schlae/a1000-scsi-sidecar/SCSISidecar.kicad_sch

## KiCad design SCSISidecar.kicad_sch (2025-05-16, an earlier design)

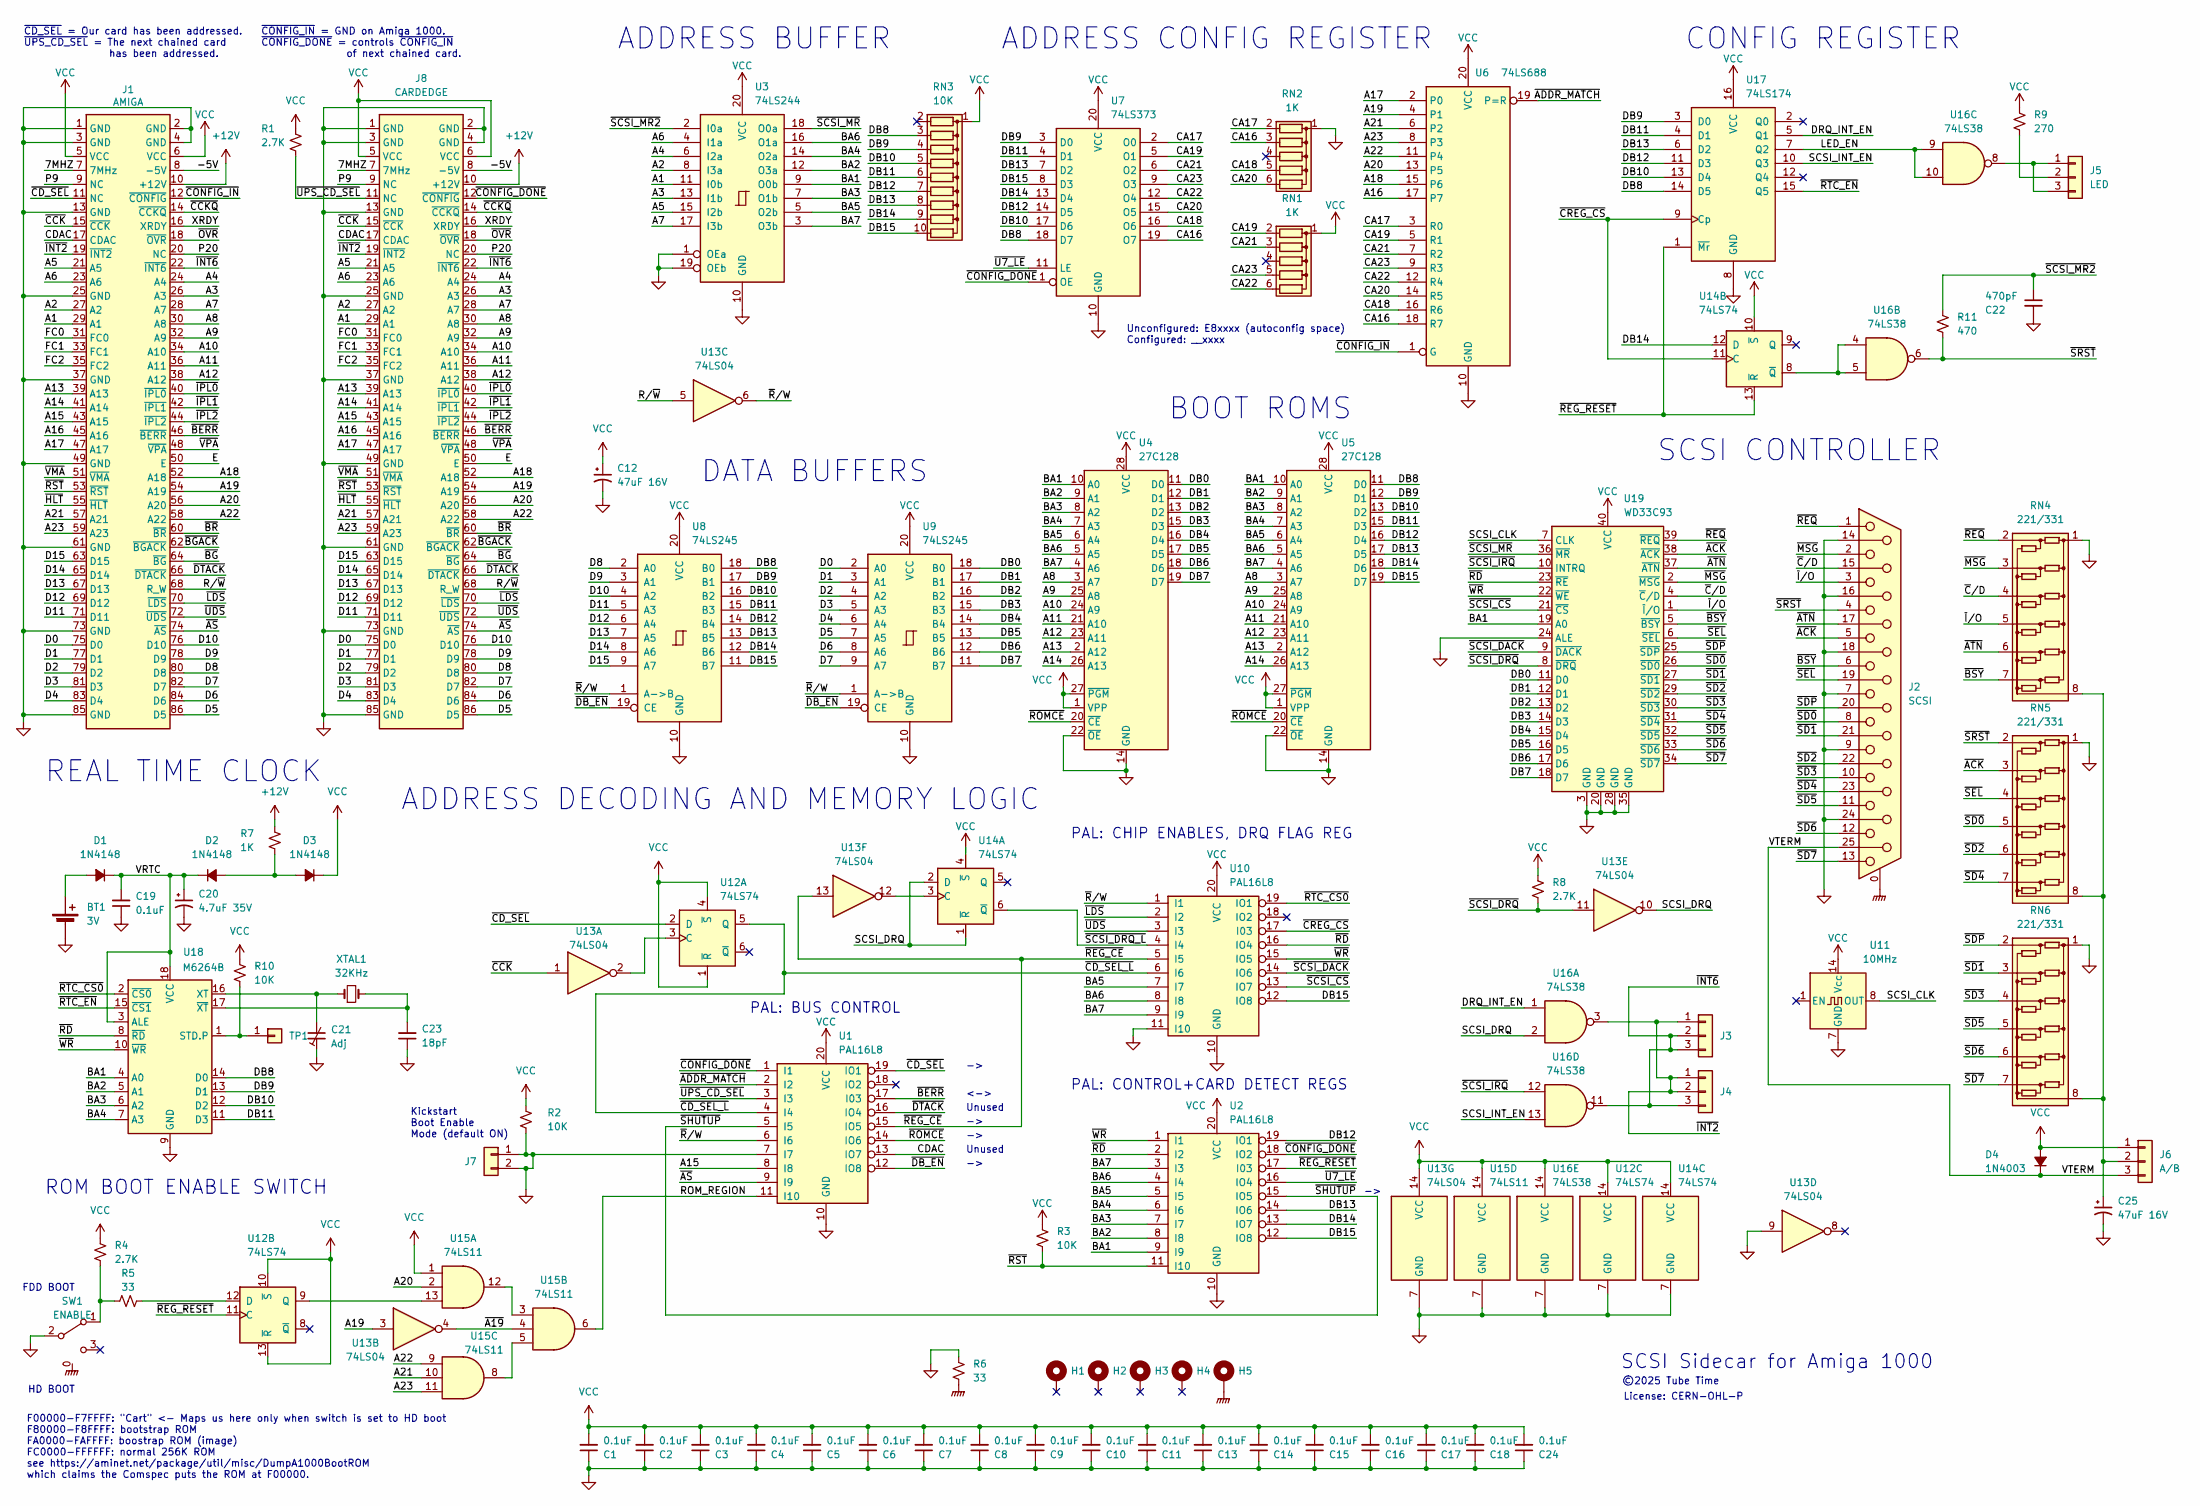
[picture p6: schematic SCSISidecar.kicad_sch]

Parts:
BT1: 3V; BatteryHolder_Keystone_104_1x23mm; MPN Keystone 104
C1, C2, C3, C4, C5, C6, C7, C8, C9, C10, C11, C13, C14, C15, C16, C17, C18, C19, C24: 0.1uF; CAPAC200
C12, C25: 47uF 16V; CAPAE200P500X1100
C20: 4.7uF 35V; CAPAE200P500X1100
C21: Adj; TRIM_CAP
C22: 470pF; CAPAC200
C23: 18pF; C_Disc_D3.0mm_W1.6mm_P2.50mm
D1, D2, D3: 1N4148; DIOA500
D4: 1N4003; DIOA500
H1, H2, H3, H4, H5: MountingHole_Pad; MountingHole_3.7mm_Pad
J1: AMIGA; TE_1-5530843-0; MPN TE 1-5530843-0 or equiv
J2: SCSI; DSUB-25_Female_Horizontal_P2.77x2.84mm_EdgePinOffset7.70mm_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
J3, J4: Conn_01x03; PinHeader_1x03_P2.54mm_Vertical
J5: LED; PinHeader_1x03_P2.54mm_Vertical
J6: A/B; PinHeader_1x03_P2.54mm_Vertical
J7: Conn_01x02; PinHeader_1x02_P2.54mm_Vertical
J8: CARDEDGE; PinHeader_2x43_P2.54mm_Vertical
R1, R4, R8: 2.7K; R_Axial_L0.26in_D0.92in_P0.5in_Horizontal
R2, R3, R10: 10K; R_Axial_L0.26in_D0.92in_P0.5in_Horizontal
R5, R6: 33; R_Axial_L0.26in_D0.92in_P0.5in_Horizontal
R7: 1K; R_Axial_L0.26in_D0.92in_P0.5in_Horizontal
R9: 270; R_Axial_L0.26in_D0.92in_P0.5in_Horizontal
R11: 470; R_Axial_L0.26in_D0.92in_P0.5in_Horizontal
RN1, RN2: 1K; R_Array_SIP6
RN3: 10K; R_Array_SIP10
RN4, RN5, RN6: 221/331; R_Array_SIP8; MPN 4608X-104-221/331L
SW1: ENABLE; SW_SPDT_RA; MPN 7101J1AV2QE2 or equiv
TP1: Conn_01x01; PinHeader_1x01_P2.54mm_Vertical
U1, U2, U10: PAL16L8; DIP254P762X635-20
U3: 74LS244; DIP254P762X635-20
U4, U5: 27C128; DIP-28_W15.24mm
U6: 74LS688; DIP254P762X635-20
U7: 74LS373; DIP254P762X635-20
U8, U9: 74LS245; DIP254P762X635-20
U11: 10MHz; Oscillator_DIP-14; MPN ECS-100AX-100 or equiv
U12, U14: 74LS74; DIP254P762X635-14
U13: 74LS04; DIP254P762X635-14
U15: 74LS11; DIP254P762X635-14
U16: 74LS38; DIP254P762X635-14
U17: 74LS174; DIP254P762X635-16
U18: M6264B; DIP254P762X635-18
U19: WD33C93; DIP254P1524X635-40
XTAL1: 32KHz; Crystal_AT310_D3.0mm_L10.0mm_Horizontal

Connections:
7MHZ: J1.7 (7MHz), J8.7 (7MHz)
+12V: J1.10 (+12V), J8.10 (+12V), R7.2
-5V: J1.8 (-5V), J8.8 (-5V)
A1: J1.29 (A1), J8.29 (A1), U3.11 (I0b)
A2: J1.27 (A2), J8.27 (A2), U3.8 (I3a)
A3: J1.26 (A3), J8.26 (A3), U3.13 (I1b)
A4: J1.24 (A4), J8.24 (A4), U3.6 (I2a)
A5: J1.21 (A5), J8.21 (A5), U3.15 (I2b)
A6: J1.23 (A6), J8.23 (A6), U3.4 (I1a)
A7: J1.28 (A7), J8.28 (A7), U3.17 (I3b)
A8: J1.30 (A8), J8.30 (A8), U4.3 (A7), U5.3 (A7)
A9: J1.32 (A9), J8.32 (A9), U4.25 (A8), U5.25 (A8)
A10: J1.34 (A10), J8.34 (A10), U4.24 (A9), U5.24 (A9)
A11: J1.36 (A11), J8.36 (A11), U4.21 (A10), U5.21 (A10)
A12: J1.38 (A12), J8.38 (A12), U4.23 (A11), U5.23 (A11)
A13: J1.39 (A13), J8.39 (A13), U4.2 (A12), U5.2 (A12)
A14: J1.41 (A14), J8.41 (A14), U4.26 (A13), U5.26 (A13)
A15: J1.43 (A15), J8.43 (A15), U1.8 (I8)
A16: J1.45 (A16), J8.45 (A16), U6.17 (P7)
A17: J1.47 (A17), J8.47 (A17), U6.2 (P0)
A18: J1.52 (A18), J8.52 (A18), U6.15 (P6)
A19: J1.54 (A19), J8.54 (A19), U6.4 (P1), U13.3
A20: J1.56 (A20), J8.56 (A20), U6.13 (P5), U15.2
A21: J1.57 (A21), J8.57 (A21), U6.6 (P2), U15.10
A22: J1.58 (A22), J8.58 (A22), U6.11 (P4), U15.9
A23: J1.59 (A23), J8.59 (A23), U6.8 (P3), U15.11
BA1: U2.9 (I9), U3.9 (O0b), U4.10 (A0), U5.10 (A0), U18.4 (A0), U19.19 (A0)
BA2: U2.8 (I8), U3.12 (O3a), U4.9 (A1), U5.9 (A1), U18.5 (A1)
BA3: U2.7 (I7), U3.7 (O1b), U4.8 (A2), U5.8 (A2), U18.6 (A2)
BA4: U2.6 (I6), U3.14 (O2a), U4.7 (A3), U5.7 (A3), U18.7 (A3)
BA5: U2.5 (I5), U3.5 (O2b), U4.6 (A4), U5.6 (A4), U10.7 (I7)
BA6: U2.4 (I4), U3.16 (O1a), U4.5 (A5), U5.5 (A5), U10.8 (I8)
BA7: U2.3 (I3), U3.3 (O3b), U4.4 (A6), U5.4 (A6), U10.9 (I9)
CA16: RN2.3 (R2), U6.18 (R7), U7.19 (O7)
CA17: RN2.2 (R1), U6.3 (R0), U7.2 (O0)
CA18: RN2.5 (R4), U6.16 (R6), U7.16 (O6)
CA19: RN1.2 (R1), U6.5 (R1), U7.5 (O1)
CA20: RN2.6 (R5), U6.14 (R5), U7.15 (O5)
CA21: RN1.3 (R2), U6.7 (R2), U7.6 (O2)
CA22: RN1.6 (R5), U6.12 (R4), U7.12 (O4)
CA23: RN1.5 (R4), U6.9 (R3), U7.9 (O3)
CDAC: J1.17 (CDAC), J8.17 (CDAC), U1.13 (IO7)
D0: J1.75 (D0), J8.75 (D0), U9.2 (A0)
D1: J1.77 (D1), J8.77 (D1), U9.3 (A1)
D2: J1.79 (D2), J8.79 (D2), U9.4 (A2)
D3: J1.81 (D3), J8.81 (D3), U9.5 (A3)
D4: J1.83 (D4), J8.83 (D4), U9.6 (A4)
D5: J1.86 (D5), J8.86 (D5), U9.7 (A5)
D6: J1.84 (D6), J8.84 (D6), U9.8 (A6)
D7: J1.82 (D7), J8.82 (D7), U9.9 (A7)
D8: J1.80 (D8), J8.80 (D8), U8.2 (A0)
D9: J1.78 (D9), J8.78 (D9), U8.3 (A1)
D10: J1.76 (D10), J8.76 (D10), U8.4 (A2)
D11: J1.71 (D11), J8.71 (D11), U8.5 (A3)
D12: J1.69 (D12), J8.69 (D12), U8.6 (A4)
D13: J1.67 (D13), J8.67 (D13), U8.7 (A5)
D14: J1.65 (D14), J8.65 (D14), U8.8 (A6)
D15: J1.63 (D15), J8.63 (D15), U8.9 (A7)
DB0: U4.11 (D0), U9.18 (B0), U19.11 (D0)
DB1: U4.12 (D1), U9.17 (B1), U19.12 (D1)
DB2: U4.13 (D2), U9.16 (B2), U19.13 (D2)
DB3: U4.15 (D3), U9.15 (B3), U19.14 (D3)
DB4: U4.16 (D4), U9.14 (B4), U19.15 (D4)
DB5: U4.17 (D5), U9.13 (B5), U19.16 (D5)
DB6: U4.18 (D6), U9.12 (B6), U19.17 (D6)
DB7: U4.19 (D7), U9.11 (B7), U19.18 (D7)
DB8: RN3.3 (R2), U5.11 (D0), U7.18 (D7), U8.18 (B0), U17.14 (D5), U18.14 (D0)
DB9: RN3.4 (R3), U5.12 (D1), U7.3 (D0), U8.17 (B1), U17.3 (D0), U18.13 (D1)
DB10: RN3.5 (R4), U5.13 (D2), U7.17 (D6), U8.16 (B2), U17.13 (D4), U18.12 (D2)
DB11: RN3.6 (R5), U5.15 (D3), U7.4 (D1), U8.15 (B3), U17.4 (D1), U18.11 (D3)
DB12: RN3.7 (R6), U2.19 (IO1), U5.16 (D4), U7.14 (D5), U8.14 (B4), U17.11 (D3)
DB13: RN3.8 (R7), U2.14 (IO6), U5.17 (D5), U7.7 (D2), U8.13 (B5), U17.6 (D2)
DB14: RN3.9 (R8), U2.13 (IO7), U5.18 (D6), U7.13 (D4), U8.12 (B6), U14.12 (D)
DB15: RN3.10 (R9), U2.12 (IO8), U5.19 (D7), U7.8 (D3), U8.11 (B7), U10.12 (IO8)
DRQ_INT_EN: U16.1, U17.5 (Q1)
E: J1.50 (E), J8.50 (E)
FC0: J1.31 (FC0), J8.31 (FC0)
FC1: J1.33 (FC1), J8.33 (FC1)
FC2: J1.35 (FC2), J8.35 (FC2)
GND: BT1.2 (-), C1.1, C2.1, C3.1, C4.1, C5.1, C6.1, C7.1, C8.1, C9.1, C10.1, C11.1, C12.2, C13.1, C14.1, C15.1, C16.1, C17.1, C18.1, C19.1, C20.2, C21.1, C22.2, C23.1, C24.1, C25.2, J1.1 (GND), J1.2 (GND), J1.3 (GND), J1.4 (GND), J1.13 (GND), J1.25 (GND), J1.37 (GND), J1.49 (GND), J1.61 (GND), J1.73 (GND), J1.85 (GND), J2.7, J2.9, J2.14, J2.16, J2.18, J2.24, J7.1, J7.2, J8.1 (GND), J8.2 (GND), J8.3 (GND), J8.4 (GND), J8.13 (GND), J8.25 (GND), J8.37 (GND), J8.49 (GND), J8.61 (GND), J8.73 (GND), J8.85 (GND), R2.1, R6.1, RN2.1 (common), RN4.1 (COM1), RN5.1 (COM1), RN6.1 (COM1), SW1.2 (B), U1.7 (I7), U1.10 (GND), U2.10 (GND), U3.1 (OEa), U3.10 (GND), U3.19 (OEb), U4.14 (GND), U4.22 (~OE), U5.14 (GND), U5.22 (~OE), U6.10 (GND), U7.10 (GND), U8.10 (GND), U9.10 (GND), U10.10 (GND), U10.11 (I10), U11.7 (GND), U12.7 (GND), U13.7 (GND), U13.9, U14.7 (GND), U15.7 (GND), U16.7 (GND), U17.8 (GND), U18.9 (GND), U19.3 (GND), U19.20 (GND), U19.24 (ALE), U19.28 (GND), U19.35 (GND)
GNDPWR: H5.1, J2.0 (PAD), R6.2, SW1.0 (SH)
LED_EN: U16.9, U16.10, U17.7 (Q2)
unnamed: BT1.1 (+), D1.2 (A)
unnamed: C21.2, U18.16 (XT), XTAL1.1
unnamed: C23.2, U18.17 (~XT), XTAL1.2
unnamed: C25.1, J6.2, RN4.8 (COM2), RN5.8 (COM2), RN6.8 (COM2)
unnamed: D2.2 (A), D3.2 (A), R7.1
unnamed: J5.1, J5.3, U16.8
unnamed: J5.2, R9.1
unnamed: R4.2, R5.2, SW1.1 (A)
unnamed: R5.1, U12.12 (D)
unnamed: R10.1, TP1.1, U18.1 (STD.P)
unnamed: U12.3 (C), U13.2
unnamed: U12.9 (Q), U15.13
unnamed: U13.12, U14.3 (C)
unnamed: U14.8 (~Q), U16.4, U16.5
unnamed: U15.5, U15.8
unnamed: U15.3, U15.12
P9: J1.9 (NC), J8.9 (NC)
P20: J1.20 (NC), J8.20 (NC)
ROM_REGION: U1.11 (I10), U15.6
R/~W: J1.68 (R_W), J8.68 (R_W), U13.5
SCSI_CLK: U11.8 (OUT), U19.7 (CLK)
SCSI_DRQ: U13.10, U14.1 (~R), U14.2 (D), U16.2
SCSI_INT_EN: U16.13, U17.10 (Q3)
VCC: C1.2, C2.2, C3.2, C4.2, C5.2, C6.2, C7.2, C8.2, C9.2, C10.2, C11.2, C12.1, C13.2, C14.2, C15.2, C16.2, C17.2, C18.2, C24.2, D3.1 (K), D4.2 (A), J1.5 (VCC), J1.6 (VCC), J6.1, J8.5 (VCC), J8.6 (VCC), R1.1, R2.2, R3.2, R4.1, R8.1, R9.2, R10.2, RN1.1 (common), RN3.1 (common), U1.20 (VCC), U2.20 (VCC), U3.20 (VCC), U4.1 (VPP), U4.27 (~PGM), U4.28 (VCC), U5.1 (VPP), U5.27 (~PGM), U5.28 (VCC), U6.20 (VCC), U7.20 (VCC), U8.20 (VCC), U9.20 (VCC), U10.20 (VCC), U11.14 (Vcc), U12.1 (~R), U12.4 (~S), U12.10 (~S), U12.13 (~R), U12.14 (VCC), U13.14 (VCC), U14.4 (~S), U14.10 (~S), U14.14 (VCC), U15.1, U15.14 (VCC), U16.14 (VCC), U17.16 (VCC), U19.40 (VCC)
VRTC: C19.2, C20.1, D1.1 (K), D2.1 (K), U18.3 (ALE), U18.18 (VCC)
VTERM: D4.1 (K), J2.25, J6.3
XRDY: J1.16 (XRDY), J8.16 (XRDY)
~A19: U13.4, U15.4
~ACK: J2.5, RN5.3 (R2), U19.38 (~ACK)
~ADDR_MATCH: U1.2 (I2), U6.19 (P=R)
~AS: J1.74 (~AS), J8.74 (~AS), U1.9 (I9)
~ATN: J2.17, RN4.6 (R5), U19.37 (~ATN)
~BERR: J1.46 (~BERR), J8.46 (~BERR), U1.17 (I03)
~BGACK: J1.62 (~BGACK), J8.62 (~BGACK)
~BG: J1.64 (~BG), J8.64 (~BG)
~BR: J1.60 (~BR), J8.60 (~BR)
~BSY: J2.6, RN4.7 (R6), U19.5 (~BSY)
~CCKQ: J1.14 (~CCKQ), J8.14 (~CCKQ)
~CCK: J1.15 (~CCK), J8.15 (~CCK), U13.1
~CD_SEL_L: U1.4 (I4), U10.6 (I6), U12.5 (Q)
~CD_SEL: J1.11 (NC), U1.19 (IO1), U12.2 (D)
~CONFIG_DONE: J8.12 (~CONFIG), U1.1 (I1), U2.18 (IO2), U7.1 (OE)
~CONFIG_IN: J1.12 (~CONFIG), U6.1 (G)
~CREG_CS: U10.17 (I03), U14.11 (C), U17.9 (Cp)
~C/D: J2.15, RN4.4 (R3), U19.4 (~C/D)
~DB_EN: U1.12 (IO8), U8.19 (CE), U9.19 (CE)
~DTACK: J1.66 (~DTACK), J8.66 (~DTACK), U1.16 (IO4)
~HLT: J1.55 (~HLT), J8.55 (~HLT)
~INT2: J1.19 (~INT2), J3.1, J4.1, J4.2, J8.19 (~INT2), U16.3
~INT6: J1.22 (~INT6), J3.2, J3.3, J4.3, J8.22 (~INT6), U16.11
~IPL0: J1.40 (~IPL0), J8.40 (~IPL0)
~IPL1: J1.42 (~IPL1), J8.42 (~IPL1)
~IPL2: J1.44 (~IPL2), J8.44 (~IPL2)
~I/O: J2.3, RN4.5 (R4), U19.1 (~I/O)
~LDS: J1.70 (~LDS), J8.70 (~LDS), U10.2 (I2)
~MSG: J2.2, RN4.3 (R2), U19.2 (~MSG)
~OVR: J1.18 (~OVR), J8.18 (~OVR)
~RD: U2.2 (I2), U10.16 (IO4), U18.8 (~RD), U19.23 (~RE)
~REG_CE: U1.15 (IO5), U10.5 (I5), U13.13
~REG_RESET: U2.17 (I03), U12.11 (C), U14.13 (~R), U17.1 (~Mr)
~REQ: J2.1, RN4.2 (R1), U19.39 (~REQ)
~ROMCE: U1.14 (IO6), U4.20 (~CE), U5.20 (~CE)
~RST: J1.53 (~RST), J8.53 (~RST), R3.1, U2.11 (I10)
~RTC_CS0: U10.19 (IO1), U18.2 (~CS0)
~RTC_EN: U17.15 (Q5), U18.15 (~CS1)
~R/W: U1.6 (I6), U8.1 (A->B), U9.1 (A->B), U10.1 (I1), U13.6
~SCSI_CS: U10.13 (IO7), U19.21 (~CS)
~SCSI_DACK: U10.14 (IO6), U19.9 (~DACK)
~SCSI_DRQ_L: U10.4 (I4), U14.6 (~Q)
~SCSI_DRQ: R8.2, U13.11, U19.8 (~DRQ)
~SCSI_IRQ: U16.12, U19.10 (INTRQ)
~SCSI_MR2: C22.1, R11.2, U3.2 (I0a)
~SCSI_MR: U3.18 (O0a), U19.36 (~MR)
~SD0: J2.8, RN5.5 (R4), U19.26 (~SD0)
~SD1: J2.21, RN6.3 (R2), U19.27 (~SD1)
~SD2: J2.22, RN5.6 (R5), U19.29 (~SD2)
~SD3: J2.10, RN6.4 (R3), U19.30 (~SD3)
~SD4: J2.23, RN5.7 (R6), U19.31 (~SD4)
~SD5: J2.11, RN6.5 (R4), U19.32 (~SD5)
~SD6: J2.12, RN6.6 (R5), U19.33 (~SD6)
~SD7: J2.13, RN6.7 (R6), U19.34 (~SD7)
~SDP: J2.20, RN6.2 (R1), U19.25 (~SDP)
~SEL: J2.19, RN5.4 (R3), U19.6 (~SEL)
~SHUTUP: U1.5 (I5), U2.15 (IO5)
~SRST: J2.4, R11.1, RN5.2 (R1), U16.6
~U7_LE: U2.16 (IO4), U7.11 (LE)
~UDS: J1.72 (~UDS), J8.72 (~UDS), U10.3 (I3)
~UPS_CD_SEL: J8.11 (NC), R1.2, U1.3 (I3)
~VMA: J1.51 (~VMA), J8.51 (~VMA)
~VPA: J1.48 (~VPA), J8.48 (~VPA)
~WR: U2.1 (I1), U10.15 (IO5), U18.10 (~WR), U19.22 (~WE)

Notes on the sheet:
BOOT ROMS
~{CD_SEL} = Our card has been addressed. ~{UPS_CD_SEL} = The next chained card has been addressed.
DATA BUFFERS
©2025 Tube Time
Unused
ROM BOOT ENABLE SWITCH
HD BOOT
License: CERN-OHL-P
Kickstart Boot Enable Mode (default ON)
PAL: BUS CONTROL
FDD BOOT
<->
SCSI Sidecar for Amiga 1000
PAL: CONTROL+CARD DETECT REGS
ADDRESS BUFFER
ADDRESS CONFIG REGISTER
ADDRESS DECODING AND MEMORY LOGIC
SCSI CONTROLLER
F00000-F7FFFF: "Cart" <- Maps us here only when switch is set to HD boot F80000-F8FFFF: bootstrap ROM FA0000-FAFFFF: boostrap ROM (image) FC0000-FFFFFF: normal 256K ROM see https://aminet.net/package/util/misc/DumpA1000BootROM which claims the Comspec puts the ROM at F00000.
CONFIG REGISTER
REAL TIME CLOCK
PAL: CHIP ENABLES, DRQ FLAG REG
~{CONFIG_IN} = GND on Amiga 1000. ~{CONFIG_DONE} = controls ~{CONFIG_IN} of next chained card.
Unconfigured: E8xxxx (autoconfig space) Configured: __xxxx
