schlae/a1000-scsi-sidecar/SideCardEdge/SideCardEdge.kicad_sch

## KiCad design SideCardEdge/SideCardEdge.kicad_sch (2025-03-26)

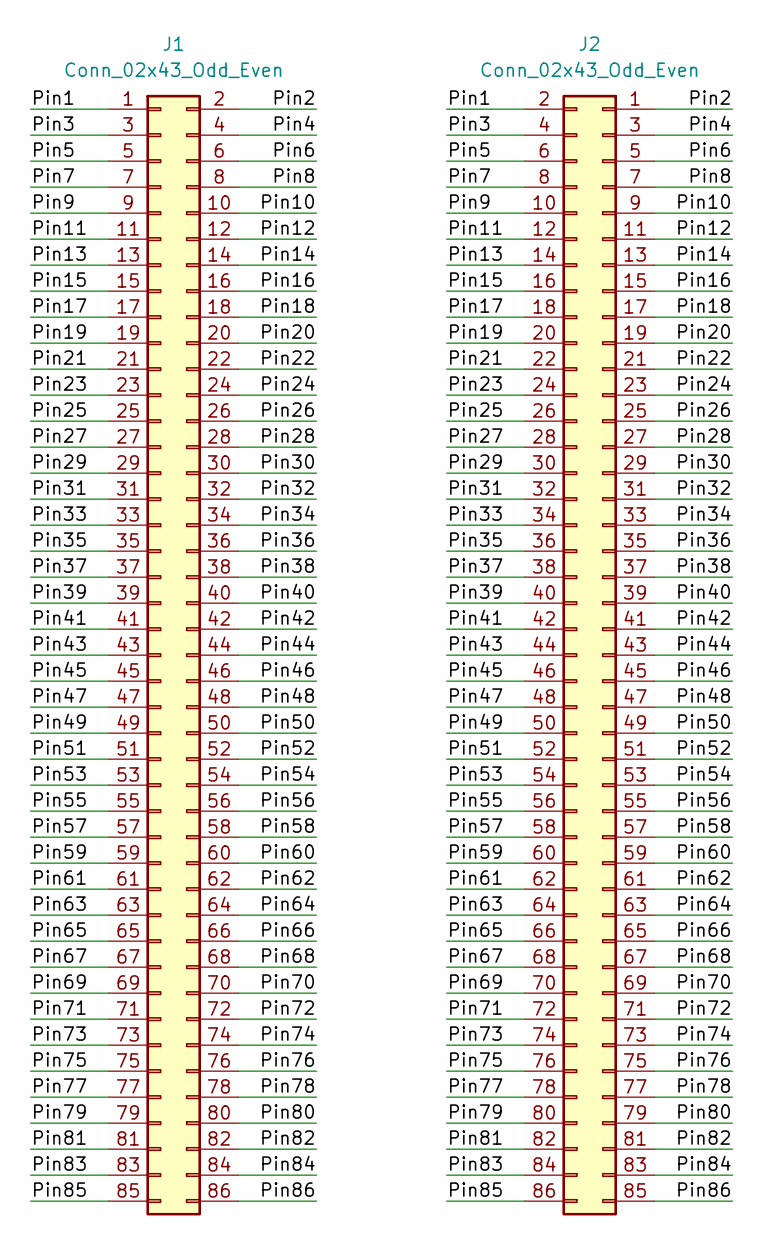
[picture p7: schematic SideCardEdge.kicad_sch]

Parts:
J1: Conn_02x43_Odd_Even; PinHeader_2x43_P2.54mm_Vertical
J2: Conn_02x43_Odd_Even; EDGE_86_100

Connections:
Pin1: J1.1, J2.2
Pin2: J1.2, J2.1
Pin3: J1.3, J2.4
Pin4: J1.4, J2.3
Pin5: J1.5, J2.6
Pin6: J1.6, J2.5
Pin7: J1.7, J2.8
Pin8: J1.8, J2.7
Pin9: J1.9, J2.10
Pin10: J1.10, J2.9
Pin11: J1.11, J2.12
Pin12: J1.12, J2.11
Pin13: J1.13, J2.14
Pin14: J1.14, J2.13
Pin15: J1.15, J2.16
Pin16: J1.16, J2.15
Pin17: J1.17, J2.18
Pin18: J1.18, J2.17
Pin19: J1.19, J2.20
Pin20: J1.20, J2.19
Pin21: J1.21, J2.22
Pin22: J1.22, J2.21
Pin23: J1.23, J2.24
Pin24: J1.24, J2.23
Pin25: J1.25, J2.26
Pin26: J1.26, J2.25
Pin27: J1.27, J2.28
Pin28: J1.28, J2.27
Pin29: J1.29, J2.30
Pin30: J1.30, J2.29
Pin31: J1.31, J2.32
Pin32: J1.32, J2.31
Pin33: J1.33, J2.34
Pin34: J1.34, J2.33
Pin35: J1.35, J2.36
Pin36: J1.36, J2.35
Pin37: J1.37, J2.38
Pin38: J1.38, J2.37
Pin39: J1.39, J2.40
Pin40: J1.40, J2.39
Pin41: J1.41, J2.42
Pin42: J1.42, J2.41
Pin43: J1.43, J2.44
Pin44: J1.44, J2.43
Pin45: J1.45, J2.46
Pin46: J1.46, J2.45
Pin47: J1.47, J2.48
Pin48: J1.48, J2.47
Pin49: J1.49, J2.50
Pin50: J1.50, J2.49
Pin51: J1.51, J2.52
Pin52: J1.52, J2.51
Pin53: J1.53, J2.54
Pin54: J1.54, J2.53
Pin55: J1.55, J2.56
Pin56: J1.56, J2.55
Pin57: J1.57, J2.58
Pin58: J1.58, J2.57
Pin59: J1.59, J2.60
Pin60: J1.60, J2.59
Pin61: J1.61, J2.62
Pin62: J1.62, J2.61
Pin63: J1.63, J2.64
Pin64: J1.64, J2.63
Pin65: J1.65, J2.66
Pin66: J1.66, J2.65
Pin67: J1.67, J2.68
Pin68: J1.68, J2.67
Pin69: J1.69, J2.70
Pin70: J1.70, J2.69
Pin71: J1.71, J2.72
Pin72: J1.72, J2.71
Pin73: J1.73, J2.74
Pin74: J1.74, J2.73
Pin75: J1.75, J2.76
Pin76: J1.76, J2.75
Pin77: J1.77, J2.78
Pin78: J1.78, J2.77
Pin79: J1.79, J2.80
Pin80: J1.80, J2.79
Pin81: J1.81, J2.82
Pin82: J1.82, J2.81
Pin83: J1.83, J2.84
Pin84: J1.84, J2.83
Pin85: J1.85, J2.86
Pin86: J1.86, J2.85
